lobapiop/Console_retro_plus/Project-CRP/docs/00-Gouvernance/CRP-Liste-Depenses.md

# Project CRP – Liste des dépenses

Version : 1.0

---

# 1. Objectif

Ce document affiche les dépenses durant le **Project CRP**.

---

- ELECROW Écran pour Raspberry Pi, Mini Moniteur 5 Pouces 1024×600 HD - 49.39 €
- db-tronic Raspberry Pi 5 4 Go NVMe Kit - 192.99 €
- UGREEN Câble Micro HDMI vers HDMI - 13.49 €
