lobapiop/Console_retro_plus/Project-CRP/docs/00-Gouvernance/Glossaire.md

| Terme | Définition |
| --- | --- |
| **Power Path** | Circuit qui gère automatiquement la bascule entre le chargeur USB-C et la batterie, tout en permettant la recharge et l'alimentation simultanées de la console. |
| **RP2040** | Microcontrôleur chargé de la gestion matérielle (Power, LED, ventilateur, batterie...). |
| **BMS** | Circuit de protection de la batterie (surcharge, décharge profonde, court-circuit...). |
| **Dock** | Station d'accueil permettant de connecter la console à une TV et de la recharger.
                                                                               |
## CAO — Conception Assistée par Ordinateur

La **CAO** désigne l’utilisation d’un logiciel pour concevoir, dessiner et vérifier des pièces ou des assemblages en deux ou trois dimensions.

Dans Project CRP, la CAO sera notamment utilisée pour créer :

- le gabarit mécanique de l’écran ;
- la coque de la console ;
- les supports internes ;
- les emplacements des boutons et des sticks ;
- les passages de câbles ;
- les trous de fixation ;
- le dock.

Le logiciel retenu pour Project CRP est **FreeCAD**, car il est libre, gratuit et adapté à un projet open source.

Une CAO détaillée ne doit être réalisée qu’à partir de dimensions fiables et vérifiées, afin d’éviter de concevoir une pièce autour d’un composant incorrectement identifié.
