lobapiop/Console_retro_plus/Project-CRP/docs/00-Gouvernance/CRP-Registre-des-decisions.md

| ID | Décision | Statut |
| --- | --- | --- |
| DEC-001 | Utilisation d’un Raspberry Pi 5 4 Go | Validée |
| DEC-002 | Batocera comme système principal | Validée |
| DEC-003 | Écran cible autour de 5 pouces | Validée |
| DEC-004 | Elecrow DLH04950B candidat prioritaire | Provisoire |
| DEC-005 | Validation finale de l’écran uniquement après test réel | Validée |
| DEC-006 | Prix non pondéré pendant l’étude technique | Validée |
| DEC-007 | Réserver 15 à 16 mm derrière l’écran en phase préliminaire | Provisoire |
