lobapiop/Console_retro_plus/Project-CRP/docs/03-Etudes-techniques/ET003-Implantation-mecanique.md

# Project CRP – Étude technique 003 – Implantation mécanique

Version : 0.1

---

## 1. Objectif

Cette étude vérifie que les différents composants peuvent être intégrés proprement dans le boîtier du projet.

## 2. Contraintes

- faible encombrement global ;
- maintien des composants sans vibration excessive ;
- bonne dissipation thermique ;
- accès simple aux connecteurs et à la batterie ;
- intégration visuelle cohérente.

## 3. Éléments à positionner

- écran ;
- carte principale ;
- batterie ;
- module audio ;
- boutons et commandes ;
- ventilateur ou système de refroidissement si nécessaire.

## 4. Recommandation provisoire

L’architecture devrait privilégier une séparation claire entre la zone d’affichage, la zone électronique et la zone batterie, afin de simplifier l’assemblage et la maintenance.

## 5. Questions ouvertes

- emplacement exact de la batterie ;
- fixation des cartes électroniques ;
- présence de renforts mécaniques ;
- accès au chargeur et aux connecteurs de dock.

## 6. Statut

Étude ouverte, à confirmer avec un prototype de boîtier.
