lobapiop/Console_retro_plus/Project-CRP/docs/03-Etudes-techniques/ET008-Dock.md

# Project CRP – Étude technique 008 – Dock

Version : 0.1

---

## 1. Objectif

Cette étude définit la logique du dock de recharge et de connexion du système Project CRP.

## 2. Contraintes

- recharge pratique du système ;
- connecteurs robustes et simples à utiliser ;
- intégration discrète dans le design ;
- compatibilité avec les fonctions de charge et de mise en veille.

## 3. Fonctions prévues

- charge de la batterie ;
- alimentation du système ;
- connexion vidéo ou USB si nécessaire ;
- maintien du boîtier en position stable.

## 4. Recommandation provisoire

Un dock simple basé sur un connecteur USB-C ou un connecteur dédié semble adapté au concept, avec une logique de charge et de mise sous tension intégrée.

## 5. Questions ouvertes

- type de connecteur à retenir ;
- nécessité d’un dock avec plusieurs ports ;
- intégration mécanique du dock dans le support.

## 6. Statut

Étude ouverte.
