lobapiop/Console_retro_plus/Project-CRP/docs/06-Tests/TEST-ET001/TEST-D02-Couleurs-contraste-et-uniformit.md

# Project CRP – TEST-D02 – Couleurs contraste et uniformité

Version : 0.1  
Statut : réalisé
Étude associée : ET001 – Module d’affichage  
Composant testé : Elecrow 5inch IPS HD Display-C 1024×600  
Référence attendue : DLH04950B  
Plateforme : Raspberry Pi 5 – 4 Go  
Système : Batocera  

---

## 1. Objectif

Évaluer les couleurs, le contraste, les dégradés et l’uniformité de la dalle.

## 2. Procédure

Afficher successivement :

- noir ;
- blanc ;
- rouge ;
- vert ;
- bleu ;
- dégradés ;
- scène sombre ;
- scène très lumineuse.

## 3. Évaluation

| Élément | Note sur 10 | Remarque |
|---|---:|---|
| Niveau de noir | 10 |  |
| Niveau de blanc | 10 |  |
| Contraste | 10 |  |
| Rouge | 10 |  |
| Vert | 10 |  |
| Bleu | 10 |  |
| Dégradés | 10 |  |
| Uniformité | 10 |  |

## 4. Défauts

| Défaut | Présent | Localisation |
|---|---|---|
| Pixel mort | non |  |
| Pixel bloqué | non |  |
| Fuite de lumière | non |  |
| Zone sombre | non |  |
| Variation de couleur | non |  |
| Bande verticale ou horizontale | non |  |

## 5. Conclusion

Résultat : Réussis
Remarques :
