lobapiop/Console_retro_plus/Project-CRP/docs/06-Tests/TEST-ET001/TEST-D03-Angles-de-vision.md

# Project CRP – TEST-D03 – Angles de vision

Version : 0.1  
Statut : réalisé 
Étude associée : ET001 – Module d’affichage  
Composant testé : Elecrow 5inch IPS HD Display-C 1024×600  
Référence attendue : DLH04950B  
Plateforme : Raspberry Pi 5 – 4 Go  
Système : Batocera  

---

## 1. Objectif

Vérifier que l’image reste lisible lorsque la console n’est pas parfaitement face à l’utilisateur.

## 2. Procédure

Observer l’écran :

- de face ;
- à environ 30° à gauche ;
- à environ 30° à droite ;
- à environ 30° au-dessus ;
- à environ 30° en dessous.

## 3. Résultats

| Position | Lisibilité | Variation des couleurs | Variation du contraste |
|---|---|---|---|
| Face | Ok | Ok | Ok |
| Gauche | Ok | Ok | Ok |
| Droite | Ok | Ok | Ok |
| Haut | Ok | Ok | Ok |
| Bas | Ok | Ok | Ok |

## 4. Conclusion

Résultat : Réussi 

Remarques :
