lobapiop/Console_retro_plus/Project-CRP/docs/06-Tests/TEST-ET001/TEST-D04-Fluidit-et-r-manence.md

# Project CRP – TEST-D04 – Fluidité et rémanence

Version : 0.1  
Statut : réalisé
Étude associée : ET001 – Module d’affichage  
Composant testé : Elecrow 5inch IPS HD Display-C 1024×600  
Référence attendue : DLH04950B  
Plateforme : Raspberry Pi 5 – 4 Go  
Système : Batocera  

---

## 1. Objectif

Rechercher les défauts visibles pendant les mouvements rapides.

## 2. Contenus à tester

- jeu 2D à défilement horizontal ;
- jeu 2D à défilement vertical ;
- jeu 3D ;
- menus Batocera ;
- scène à mouvements rapides.

## 3. Résultats

| Élément | Résultat |
|---|---|
| Défilement fluide | Oui |
| Déchirure d’image visible | Non |
| Rémanence visible | Non |
| Saccades liées à l’affichage | Non |
| Scintillement | Non |
| Perte temporaire du signal | Non |

## 4. Conclusion

Résultat : Réussi

Remarques :
