lobapiop/Console_retro_plus/Project-CRP/docs/06-Tests/TEST-ET001/TEST-E01-Interface-EmulationStation.md

# Project CRP – TEST-E01 – Interface EmulationStation

Version : 0.1  
Statut : réalisé
Étude associée : ET001 – Module d’affichage  
Composant testé : Elecrow 5inch IPS HD Display-C 1024×600  
Référence attendue : DLH04950B  
Plateforme : Raspberry Pi 5 – 4 Go  
Système : Batocera  

---

## 1. Objectif

Vérifier la lisibilité et l’usage normal de l’interface Batocera.

## 2. Procédure

Naviguer dans :

- l’écran principal ;
- les listes de systèmes ;
- les listes de jeux ;
- les menus de paramètres ;
- les boîtes de dialogue.

## 3. Résultats

| Contrôle | Conforme | Remarque |
|---|---|---|
| Textes lisibles | Oui |  |
| Menus entièrement visibles | Oui |  |
| Icônes correctement dimensionnées | Oui |  |
| Aucun élément coupé | Oui |  |
| Navigation fluide | Oui |  |
| Fenêtres de dialogue lisibles | Oui |  |
| Réglages accessibles | Oui |  |

## 4. Évaluation

Note de lisibilité sur 10 : 10

## 5. Conclusion

Résultat : Réussi 

Remarques :
