lobapiop/Console_retro_plus/Project-CRP/docs/06-Tests/TEST-ET001/TEST-E02-Jeux-r-tro-au-format-4-sur-3.md

# Project CRP – TEST-E02 – Jeux rétro au format 4 sur 3

Version : 0.1  
Statut : réalisé
Étude associée : ET001 – Module d’affichage  
Composant testé : Elecrow 5inch IPS HD Display-C 1024×600  
Référence attendue : DLH04950B  
Plateforme : Raspberry Pi 5 – 4 Go  
Système : Batocera  

---

## 1. Objectif

Vérifier le rendu des principaux systèmes rétro conçus pour un écran 4:3.

## 2. Systèmes conseillés

- NES ;
- Super Nintendo ;
- Mega Drive ;
- PlayStation ;
- Nintendo 64.

## 3. Résultats

| Contrôle | Conforme | Remarque |
|---|---|---|
| Proportions respectées | Oui |  |
| Bordures acceptables | Oui |  |
| Pixels nets | Oui |  |
| Texte en jeu lisible | Oui |  |
| Aucun recadrage | Non |  |
| Fluidité satisfaisante | Oui |  |

## 4. Jeux utilisés

| Système | Jeu | Résultat |
|---|---|---|
| Super Nintendo | Classic Kong | ok |
| Ports | Doom | ok |
| DS | Pokemon Or | ok |

## 5. Conclusion

Résultat : Réussi 

Remarques : Pour les jeux, l'écran était un peu petit j'ai du faire du paramétrage pour avoir un écran un peu plus confort. Le paramètrage n'est pas terrible mais j'ai pas passé beaucoup de temps pour trouver le bon.
