lobapiop/Console_retro_plus/Project-CRP/docs/06-Tests/TEST-ET001/TEST-E03-Jeux-au-format-large.md

# Project CRP – TEST-E03 – Jeux au format large

Version : 0.1  
Statut : réalisé 
Étude associée : ET001 – Module d’affichage  
Composant testé : Elecrow 5inch IPS HD Display-C 1024×600  
Référence attendue : DLH04950B  
Plateforme : Raspberry Pi 5 – 4 Go  
Système : Batocera  

---

## 1. Objectif

Vérifier le comportement des contenus 16:9 ou proches du format de l’écran.

## 2. Résultats

| Contrôle | Conforme | Remarque |
|---|---|---|
| Utilisation correcte de la surface | Oui |  |
| Image non déformée | Non |  |
| Menus lisibles | Oui |  |
| Fluidité satisfaisante | Oui |  |
| Aucun recadrage gênant | Oui |  |

## 3. Jeux utilisés

| Système | Jeu | Résultat |
|---|---|---|
| PSP | Burnout Legends | ok |
| PSP | GTA Liberty city Stories | Ok |

## 4. Conclusion

Résultat : Réussi

Remarques :
