lobapiop/Console_retro_plus/Project-CRP/docs/06-Tests/TEST-ET001/TEST-I01-Fonctionnement-prolong-et-temp-rature.md

# Project CRP – TEST-I01 – Fonctionnement prolongé et température

Version : 0.1  
Statut : réalisé 
Étude associée : ET001 – Module d’affichage  
Composant testé : Elecrow 5inch IPS HD Display-C 1024×600  
Référence attendue : DLH04950B  
Plateforme : Raspberry Pi 5 – 4 Go  
Système : Batocera  

---

## 1. Objectif

Vérifier la stabilité de l’écran pendant une heure d’utilisation variée.

## 2. Séquence

- 15 minutes dans les menus ;
- 15 minutes sur un jeu 2D ; classic kong
- 15 minutes sur un jeu 3D ; Crash bandicoot
- 15 minutes sur Nintendo DS ou un émulateur exigeant. Pokemon or hearth gold

## 3. Relevés

| Temps | État de l’image | Température écran | Température Pi | Défaut |
|---:|---|---:|---:|---|
| 0 min | Ok | froid  | 40800 |  |
| 15 min | Ok | froid | 40800 |  |
| 30 min | Ok | froid | 48500 |  |
| 45 min | Ok | froid | 49050 |  |
| 60 min | Ok | froid | 55100 |  |

## 4. Points à surveiller

- perte du signal ;
- scintillement ;
- baisse de luminosité ;
- lignes parasites ;
- blocage tactile ;
- redémarrage ;
- odeur inhabituelle ;
- composant anormalement chaud.

## 5. Conclusion

Résultat : Réussi 

Remarques :
